BitMaker-hub/Seeder/src/workflow.cpp

#include <Arduino.h>
#include "gpio.h"
#include "btc.h"
#include "GlobalVARS.h"
#include "workflow.h"
#include "ui/ui.h"

/**********************🍃 GLOBAL Vars *******************************/
extern sWallet myWallet;
extern sButton btnMove;
extern sButton btnSelect;

int menuSeed = SHOW_SEED1;
uint8_t entropy[32];               //Entropía cruda que aporta el usuario
char diceRolls[DICE_MAX_ROLLS+1];  //Dígitos ASCII de las tiradas
uint8_t diceValue = 1;             //Valor que se está marcando ahora
uint8_t rollHist[3] = {0,0,0};     //Tres últimas tiradas, la más reciente al final

/**************🍃 HELPERS *****************/
uint8_t entropyBytes(void){ return myWallet.nWords * 4 / 3; }
uint8_t diceRollsNeeded(void){ return (myWallet.nWords == 12) ? DICE_ROLLS_12 : DICE_ROLLS_24; }

//Con 12 palabras no hay segunda página de mnemónico, así que las siguientes
//bajan un número en vez de saltárselo
static uint8_t seedSteps(void){ return (myWallet.nWords == 12) ? SHOW_EXPORTZPUB-1 : SHOW_EXPORTZPUB; }
static uint8_t seedStep(void) { return (myWallet.nWords == 12 && menuSeed > SHOW_SEED2) ? menuSeed-1 : menuSeed; }

//Asignar "" sólo pone la longitud a cero: el texto se queda en el buffer
static void wipeString(String &s){
  for(unsigned int i = 0; i < s.length(); i++) s[i] = '\0';
  s = "";
}

//Todo lo que permitiría reconstruir la semilla. uBitcoin ya hace memzero de
//la clave privada y del chain code al destruirlas.
void wipeSeed(void){
  wipeString(myWallet.mnemonic);
  wipeString(myWallet.entropyHex);
  wipeString(myWallet.xpub);
  wipeString(myWallet.fingerprint);
  wipeString(myWallet.firstAddress);
  memset(entropy,   0, sizeof(entropy));
  memset(diceRolls, 0, sizeof(diceRolls));
  myWallet.nBCoinEntropy = 0;
  myWallet.nRolls = 0;
  diceValue = 1; memset(rollHist, 0, sizeof(rollHist));
}

//Siempre antes de capturar: entropy[] es global y si no arrastraría bits de
//una semilla anterior, y el resultado dejaría de ser verificable.
void resetEntropy(void){
  memset(entropy, 0, sizeof(entropy));
  myWallet.nBCoinEntropy = 0;
}

void drawInitMenu(void) { ui::menu(myWallet.entropySrc == diceEntropy); }
void drawWordsMenu(void){ ui::words(myWallet.nWords); }

/* Lo que va en el QR de solo lectura. Aislado aqui a proposito: de que
   exactamente traga Sparrow depende el largo, y el largo decide el tamano del
   modulo en la pantalla pequena. */
static String watchOnlyExport(void){
  return myWallet.xpub;
}

static void drawSeedPage(void){
  const uint8_t st = seedStep(), tot = seedSteps();
  switch(menuSeed){
    case SHOW_SEED1:    ui::mnemonic(myWallet.mnemonic, myWallet.nWords, 0,  st, tot); break;
    case SHOW_SEED2:    ui::mnemonic(myWallet.mnemonic, myWallet.nWords, 12, st, tot); break;
    case SHOW_DATA1:    ui::seedAddress(myWallet.firstAddress, st, tot); break;
    case SHOW_ENTROPY:  ui::seedEntropy(myWallet.entropyHex, st, tot); break;
    case SHOW_EXPORTQR: ui::seedQr(myWallet.mnemonic, myWallet.nWords); break;
    case SHOW_EXPORTZPUB: ui::seedZpubQr(watchOnlyExport(), myWallet.fingerprint); break;
    case SHOW_EXIT:     ui::seedExit(); break;
  }
}

/* Durante la captura no habia forma de volver atras salvo desconectar, y a
   mitad de 99 tiradas eso es una trampa. Mantener OK vuelve al menu.

   Se arma con LongClick y no con un contador propio porque ese evento es el
   que ya anula el click de la suelta: soltar a mitad del aviso no puede
   colar un bit ni una tirada que el usuario acababa de descartar. */
static bool holdArmed = false;

static void redrawCapture(void){
  if(myWallet.State == STATE_COINSEED){
    const uint16_t bits = entropyBytes() * 8;
    ui::coinEnter(bits);
    ui::coinUpdate(myWallet.nBCoinEntropy, bits, entropy);
  }else{
    const uint8_t total = diceRollsNeeded();
    ui::diceEnter(total);
    ui::diceUpdate(myWallet.nRolls, total, diceValue, rollHist);
  }
}

//true = el ciclo ya esta servido; mientras el aviso esta puesto no responde
//nada mas de la pantalla, tampoco MOVE
static bool holdToStartOver(void){
  const int sel = btnSelect.click();

  if(sel == HoldClick){
    holdArmed = false;
    wipeSeed();                       //lo capturado a medias no sobrevive
    myWallet.State = STATE_INITMENU;
    drawInitMenu();
    return true;
  }

  if(sel == LongClick){ holdArmed = true; ui::holdEnter(); }
  if(!holdArmed) return false;

  const unsigned long held = btnSelect.heldMs();
  if(!held){                          //solto antes de tiempo: sigue donde estaba
    holdArmed = false;
    redrawCapture();
    return true;
  }
  ui::holdUpdate(held > BTN_LONG_MS
                   ? (float)(held - BTN_LONG_MS) / (BTN_HOLD_MS - BTN_LONG_MS)
                   : 0.0f);
  return true;
}

static void generateSeed(void){
  ui::generating();
  createSeed(myWallet.nWords, entropy);
  myWallet.State = STATE_SEED;
  menuSeed = SHOW_SEED1;
  drawSeedPage();
}

/**************🍃 WORKSATES *********************
  🍃🍃🍃🍃🍃🍃🍃🍃🍃🍃🍃🍃🍃🍃🍃🍃🍃🍃🍃🍃🍃🍃🍃🍃🍃🍃🍃
 ***********************************************/

/**************🍃 INITIAL MENU *****************/
/* Todos los estados comparan el tipo de click y nunca su verdad: hay mas de
   un evento por pulsacion y un mantenido no puede colarse donde se esperaba
   un toque. */
void doInitMenu(void){
  if(btnMove.click() == SingleClick){
    myWallet.entropySrc = (myWallet.entropySrc == coinEntropy) ? diceEntropy : coinEntropy;
    drawInitMenu();
  }
  if(btnSelect.click() == SingleClick){
    myWallet.nWords = 12;
    myWallet.State  = STATE_WORDS;
    drawWordsMenu();
  }
}

/**************🍃 SELECT WORDS *****************/
void doMenuWords(void){
  if(btnMove.click() == SingleClick){
    myWallet.nWords = (myWallet.nWords == 12) ? 24 : 12;
    drawWordsMenu();
  }
  if(btnSelect.click() == SingleClick){
    resetEntropy();
    if(myWallet.entropySrc == coinEntropy){
      myWallet.State = STATE_COINSEED;
      ui::coinEnter(entropyBytes()*8);
      ui::coinUpdate(0, entropyBytes()*8, entropy);
    }else{
      myWallet.State  = STATE_DICESEED;
      myWallet.nRolls = 0;
      diceValue = 1;
      memset(diceRolls, 0, sizeof(diceRolls));
      memset(rollHist,  0, sizeof(rollHist));
      ui::diceEnter(diceRollsNeeded());
      ui::diceUpdate(0, diceRollsNeeded(), diceValue, rollHist);
    }
  }
}

/**************🍃 COIN ENTROPY *****************/
void doCoinSeed(void){
  if(holdToStartOver()) return;

  const int mv = btnMove.click(), sel = btnSelect.click();
  if(mv != SingleClick && sel != SingleClick) return;

  const uint16_t maxBits = entropyBytes() * 8;
  const uint8_t  coin    = (mv == SingleClick) ? 1 : 0;

  //OR, nunca sumar: sumar arrastraría acarreos a los bits vecinos
  entropy[myWallet.nBCoinEntropy/8] |= (coin << (7 - myWallet.nBCoinEntropy%8));
  myWallet.nBCoinEntropy++;

  ui::coinUpdate(myWallet.nBCoinEntropy, maxBits, entropy);

  //Comprobado DESPUÉS de incrementar: llegar a 0 en pantalla significa
  //"ya está", no "una tirada más"
  if(myWallet.nBCoinEntropy >= maxBits) generateSeed();
}

/**************🍃 DICE ENTROPY *****************/
void doDiceSeed(void){
  if(holdToStartOver()) return;

  const uint8_t total = diceRollsNeeded();

  if(btnMove.click() == SingleClick){
    diceValue = (diceValue % 6) + 1;   //1..6, da la vuelta
    ui::diceUpdate(myWallet.nRolls, total, diceValue, rollHist);
  }

  if(btnSelect.click() == SingleClick){
    diceRolls[myWallet.nRolls++] = '0' + diceValue;
    rollHist[0] = rollHist[1]; rollHist[1] = rollHist[2]; rollHist[2] = diceValue;
    diceValue = 1;

    if(myWallet.nRolls >= total){
      entropyFromDice(diceRolls, myWallet.nRolls, entropy);
      generateSeed();
      return;
    }
    ui::diceUpdate(myWallet.nRolls, total, diceValue, rollHist);
  }
}

/**************🍃 SHOW SEED *****************/
//MOVE avanza, OK retrocede, ambos dan la vuelta. Salir es deliberado: sólo
//desde la última página y sólo manteniendo pulsado, para que nadie se salga
//de la semilla por accidente antes de haberla apuntado.
static void seedPageStep(int dir){
  do{
    menuSeed += dir;
    if(menuSeed > SHOW_EXIT)  menuSeed = SHOW_SEED1;
    if(menuSeed < SHOW_SEED1) menuSeed = SHOW_EXIT;
  }while(myWallet.nWords == 12 && menuSeed == SHOW_SEED2);
  drawSeedPage();
}

void doShowSeed(void){
  if(btnMove.click() == SingleClick) seedPageStep(+1);

  const int sel = btnSelect.click();
  if(sel == LongClick && menuSeed == SHOW_EXIT){
    wipeSeed();
    myWallet.State = STATE_INITMENU;
    drawInitMenu();
  }
  else if(sel == SingleClick) seedPageStep(-1);
}
