BitMaker-hub/Seeder/src/GlobalVARS.h

#include <stdint.h>
#include <Arduino.h>

#define byte uint8_t

/**********************************
 🍃 DEFINITIONS
**********************************/
enum { coinEntropy, diceEntropy };
/**********************************
 🍃 DEBUG
 The T-Display is powered over USB, so ANYTHING printed here ends up on the
 host PC. The mnemonic and the raw entropy are never printed, at any level.
 This flag only enables harmless UI traces (button events).
**********************************/
#define SEEDER_DEBUG      0

#if SEEDER_DEBUG
  #define DBGLN(x)        Serial.println(x)
#else
  #define DBGLN(x)        do{}while(0)
#endif

/**********************************
 🍃 GENERAL
**********************************/
#define SERIAL_BAUD       115200   // baudrate debug

// The seed is NEVER written to flash: it only ever lives in RAM and a power
// cycle wipes it. That is deliberate - do not add persistence here.

/***************🍃 PLACA ***************/
/* Pines y dimensiones vienen de src/boards/, no de aquí */
#include "boards/board.h"

/********** 🍃 STATES ************************/
#define STATE_INITMENU    1
#define STATE_WORDS       2
#define STATE_SEED        3
#define STATE_COINSEED    4
#define STATE_DICESEED    5
/********** 🍃 SHOW SEED PARAMS ************************/
#define SHOW_SEED1        1
#define SHOW_SEED2        2
#define SHOW_DATA1        3
#define SHOW_ENTROPY      4
#define SHOW_EXPORTQR     5
#define SHOW_EXPORTZPUB   6
#define SHOW_EXIT         7
/********** 🍃 DICE ************************/
// Same scheme as Coldcard: the ASCII digits of the rolls are hashed with
// SHA-256. A d6 carries log2(6) = 2.585 bits, so 50 rolls = 129.2 bits and
// 99 rolls = 255.9 bits. Verify offline with:  printf '3141...' | sha256sum
#define DICE_ROLLS_12     50
#define DICE_ROLLS_24     99
#define DICE_MAX_ROLLS    99
/**********************************/

//🍃 Global vars 
typedef struct {
   uint8_t State;           //SEEDER current menu position
   uint8_t entropySrc;      //Where the entropy comes from: coinEntropy | diceEntropy
   uint8_t nWords;          //Current number of Words selected on wallet
   uint16_t nBCoinEntropy;  //Bits of entropy captured so far (24 words needs 256, does not fit in uint8_t)
   uint8_t nRolls;          //Dice rolls entered so far
   String xpub;             //Current account zpub
   String fingerprint;      //Huella de la clave maestra, para el descriptor
   String firstAddress;     //m/84'/0'/0'/0/0
   String mnemonic;         //Current words
   String entropyHex;       //Entropy the seed was derived from, shown for offline verification
}sWallet;


/*********************************************************************************
**                            End Of File
*********************************************************************************/
