BitMaker-hub/Seeder/src/workflow.h

#pragma once
#include <Arduino.h>

/**********🍃 WORKFLOW FUNCTIONS ****************/
void doInitMenu(void);
void doMenuWords(void);
void doShowSeed(void);
void doCoinSeed(void);
void doDiceSeed(void);
void drawInitMenu(void);
void drawWordsMenu(void);
