BitMaker-hub/Seeder/src/ui/brand.h

#pragma once
#include <stdint.h>
#include <pgmspace.h>

/**********************************
 🍃 MARCA
 Recortes del arte original, no reinterpretaciones:

 - seederMark: el logotipo de la pantalla de arranque (x 55..188, y 13..38),
   con su suavizado recalculado sobre el verde de la franja en vez de
   umbralizado, que era lo que lo dejaba dentado.
 - leafMark: la hoja de la cabecera antigua, recortada en color. El fondo de
   aquella cabecera es exactamente este mismo verde, así que es el dibujo
   original tal cual.
**********************************/

const uint16_t seederMarkWidth  = 134;
const uint16_t seederMarkHeight = 26;
const unsigned short seederMark[3484] PROGMEM = {
  0x86F3, 0x86F3, 0x86F3, 0x86F3, 0x86F3, 0x86F3, 0x6DD0, 0x4BCA, 0x2A67, 0x21C5, 0x1984, 0x19A4,
  0x2A26, 0x3B08, 0x546C, 0x7611, 0x86F3, 0x86F3, 0x86F3, 0x86F3, 0x86F3, 0x86F3, 0x86F3, 0x656F,
  0x2A26, 0x3287, 0x3287, 0x3287, 0x3287, 0x3287, 0x3287, 0x3287, 0x3287, 0x3287, 0x3287, 0x3287,
  0x3287, 0x3287, 0x3287, 0x2A67, 0x32C7, 0x7E92, 0x86F3, 0x86F3, 0x656F, 0x2A26, 0x3287, 0x3287,
  0x3287, 0x3287, 0x3287, 0x3287, 0x3287, 0x3287, 0x3287, 0x3287, 0x3287, 0x3287, 0x3287, 0x3287,
  0x2A66, 0x32E8, 0x7EB2, 0x86F3, 0x86F3, 0x652E, 0x2A26, 0x3287, 0x3287, 0x3287, 0x3287, 0x3287,
  0x3287, 0x3287, 0x3287, 0x3287, 0x32C7, 0x4389, 0x546C, 0x7610, 0x86F3, 0x86F3, 0x86F3, 0x86F3,
  0x86F3, 0x86F3, 0x86F3, 0x86F3, 0x86F3, 0x86F3, 0x6DF0, 0x2A46, 0x2A67, 0x3287, 0x3287, 0x3287,
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
  0x3287, 0x86F3, 0x86F3, 0x86F3, 0x86F3, 0x86F3, 0x86F3, 0x86F3, 0x86F3, 0x86F3, 0x86F3, 0x86F3,
  0x86F3, 0x86F3, 0x86F3, 0x86F3, 0x86F3, 0x652E, 0x2A26, 0x10C2, 0x0000, 0x0000, 0x0000, 0x0000,
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
};
