BitMaker-hub/Seeder/src/ui/ui.h

#pragma once
#include <Arduino.h>

/**********************************
 🍃 CAPA DE PINTADO
 workflow.cpp llama a estas funciones y no toca un solo píxel. Cada una
 recibe los datos que necesita y decide cómo se ven.
**********************************/

namespace ui {

/*** Piezas reutilizables, expuestas por si hacen falta fuera ***/
void tiny(const char *s, int x, int y, uint16_t col, char datum='L', int sp=0, uint8_t size=1);
void die(int x, int y, int size, uint8_t value, uint16_t col);
void coin(int x, int y, int size, uint16_t col);
void caret(int cx, int y, int w, int h, uint16_t col);
void bar(int x, int y, int w, int h, float frac);

/*** Pantallas ***/
void splash(void);
void menu(bool diceSelected);
void words(uint8_t nWords);

void coinEnter(uint16_t totalBits);
void coinUpdate(uint16_t done, uint16_t totalBits, const uint8_t *entropy);

void diceEnter(uint8_t totalRolls);
void diceUpdate(uint8_t done, uint8_t totalRolls, uint8_t value, const uint8_t *hist);

/* Aviso de "mantener OK para empezar de nuevo". Se pinta encima de la
   captura, de ahi que vayan separadas: holdEnter() una vez y holdUpdate()
   en cada vuelta del bucle, que si no la barra parpadea. */
void holdEnter(void);
void holdUpdate(float frac);

void generating(void);

void mnemonic(const String &mn, uint8_t nWords, uint8_t from, uint8_t step, uint8_t total);
void seedAddress(const String &addr, uint8_t step, uint8_t total);
void seedEntropy(const String &hex, uint8_t step, uint8_t total);
void seedQr(const String &data, uint8_t nWords);
void seedZpubQr(const String &data, const String &fingerprint);
void seedExit(void);

}  // namespace ui
